agkaminski/FellaPC/firmware/system.h

/* FellaPC Firmaware
 * System init
 * Copyright: Aleksander Kaminski, 2024
 * See LICENSE.md
 */

#ifndef SYSTEM_H_
#define SYSTEM_H_

#include <stdint.h>

uint16_t system_time(void);

void system_init(void);

#endif
