agkaminski/FellaPC/firmware/cmd.h

/* FellaPC Firmaware
 * Command handling
 * Copyright: Aleksander Kaminski, 2024
 * See LICENSE.md
 */

#ifndef CMD_H_
#define CMD_H_

struct line {
	struct line *next;
	int number;
	char data[];
};

void cmd_die(int8_t err) __attribute__ ((noreturn));

int8_t cmd_parse(const char *cmd);

#endif
